mlab-modules/OLED01/doc/gen/dxf/OLED01-B_Fab.dxf

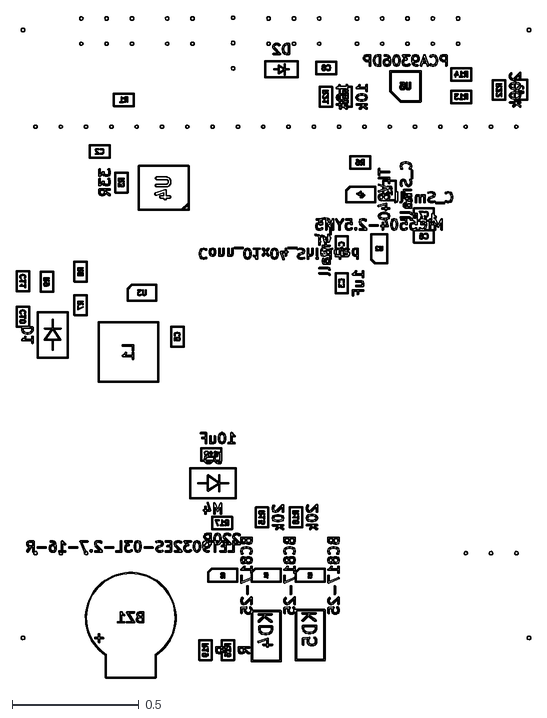
[picture p10: CAD file, 2025-04-12]
doc/gen/dxf/OLED01-B_Fab.dxf
2.03 x 2.62
