mlab-modules/OLED01/doc/gen/dxf/OLED01-F_Fab.dxf

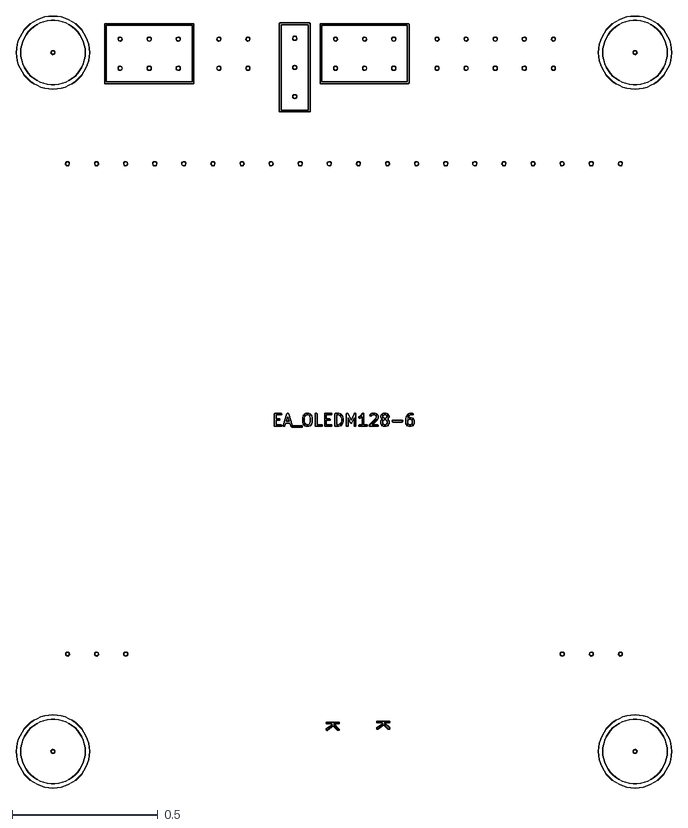
[picture p11: CAD file, 2025-04-12]
doc/gen/dxf/OLED01-F_Fab.dxf
2.25 x 2.65
